saimadhav101022/Digital_twin_robotic_arm/Digital_twin_pictures/1.jpeg

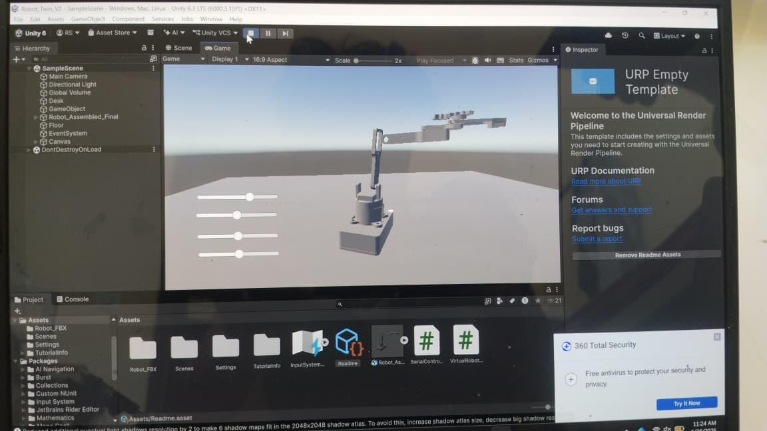
Digital_twin_pictures/1.jpeg
