saimadhav101022/Digital_twin_robotic_arm/Digital_twin_pictures/2 (2).jpeg

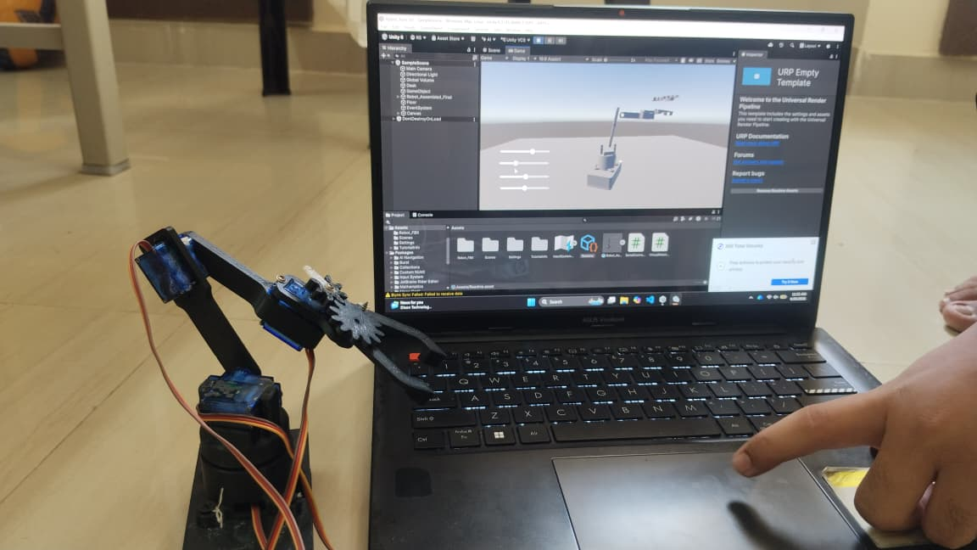
Digital_twin_pictures/2 (2).jpeg
