saimadhav101022/Digital_twin_robotic_arm/Digital_twin_pictures/2 (7).jpeg

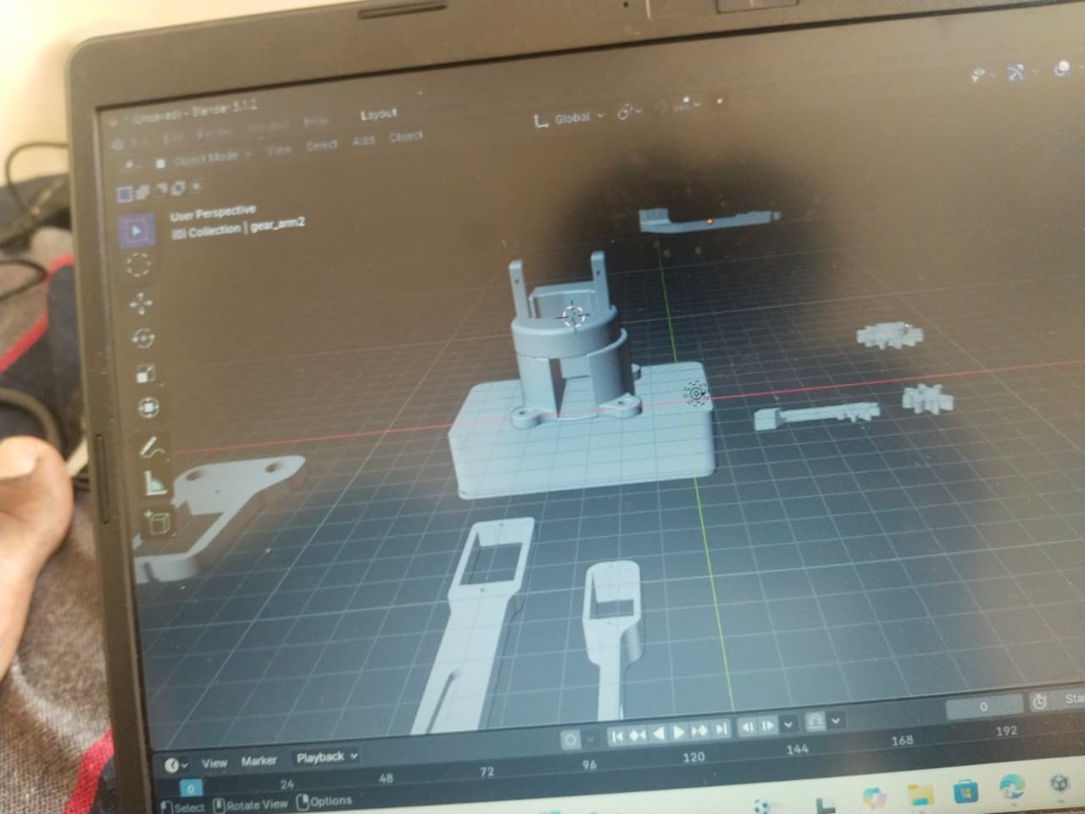
Digital_twin_pictures/2 (7).jpeg
