saimadhav101022/Digital_twin_robotic_arm/PCB_version/1.jpeg

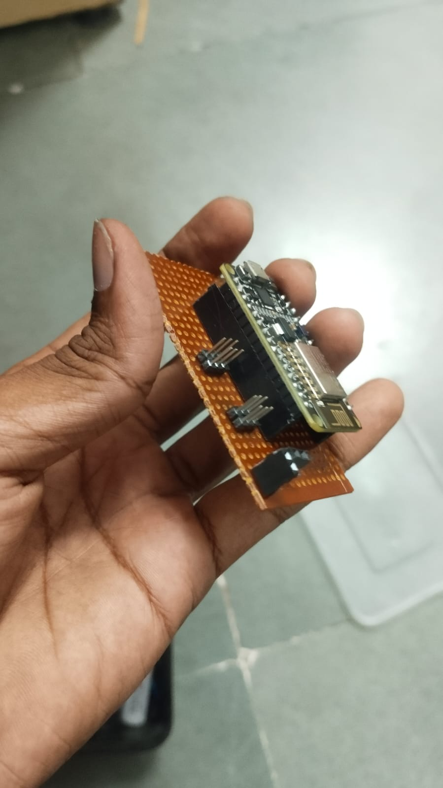
PCB_version/1.jpeg
