saimadhav101022/Digital_twin_robotic_arm/pictures_videos/WhatsApp Image 2026-07-18 at 1.06.55 PM.jpeg

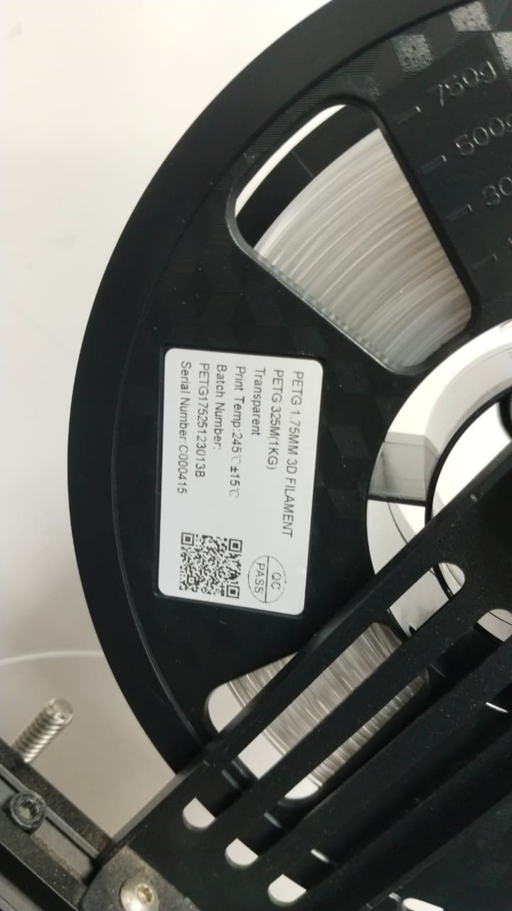
pictures_videos/WhatsApp Image 2026-07-18 at 1.06.55 PM.jpeg
